jgeurten/Hollow-Organ/CAD/SLDPRTs/MCU_Battery_shield.SLDPRT

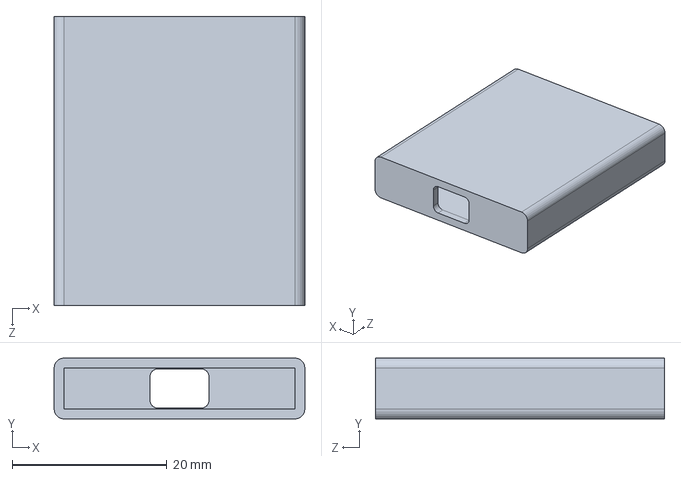
[picture p20: CAD file, 2017-09-10]
CAD/SLDPRTs/MCU_Battery_shield.SLDPRT
32.4 x 7.87 x 37.3 mm
