jgeurten/Hollow-Organ/CAD/SLDPRTs/pushbutton_panel.SLDPRT

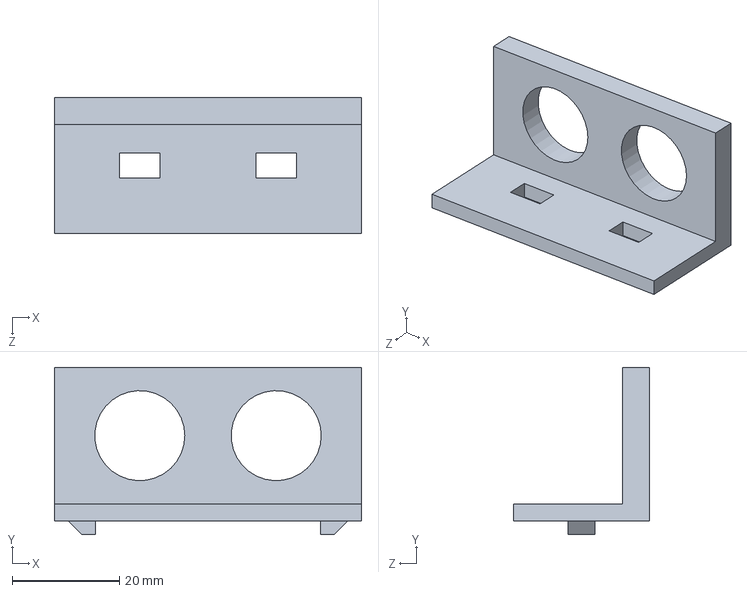
[picture p21: CAD file, 2017-09-10]
CAD/SLDPRTs/pushbutton_panel.SLDPRT
57.1 x 31.1 x 25.4 mm
