jgeurten/Hollow-Organ/CAD/SLDPRTs/bearing.SLDPRT

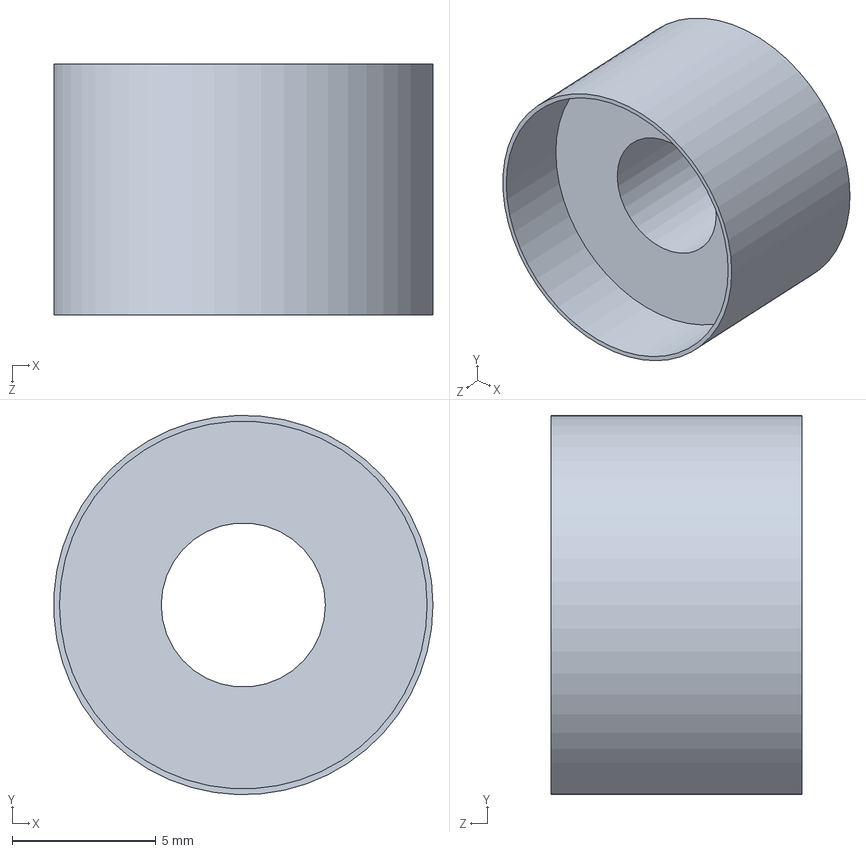
[picture p22: CAD file, 2017-09-10]
CAD/SLDPRTs/bearing.SLDPRT
13.2 x 13.2 x 8.74 mm
