jgeurten/Hollow-Organ/CAD/SLDPRTs/sphere.SLDPRT

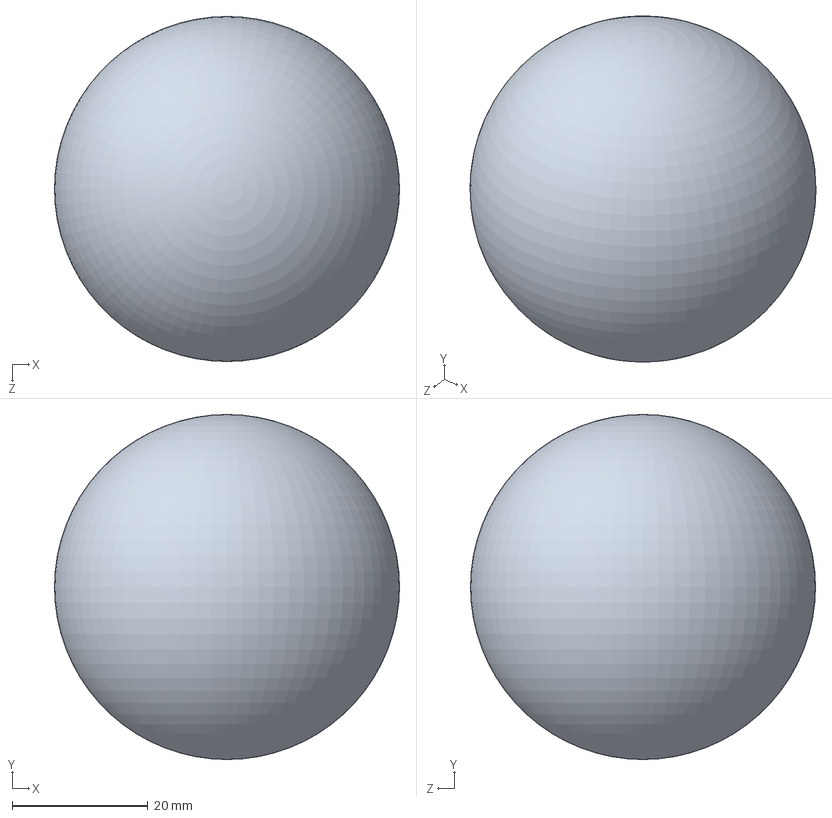
[picture p23: CAD file, 2017-09-10]
CAD/SLDPRTs/sphere.SLDPRT
50.8 x 50.8 x 50.8 mm
