jgeurten/Hollow-Organ/CAD/SLDPRTs/Face_Shaft_Collar_revE.SLDPRT

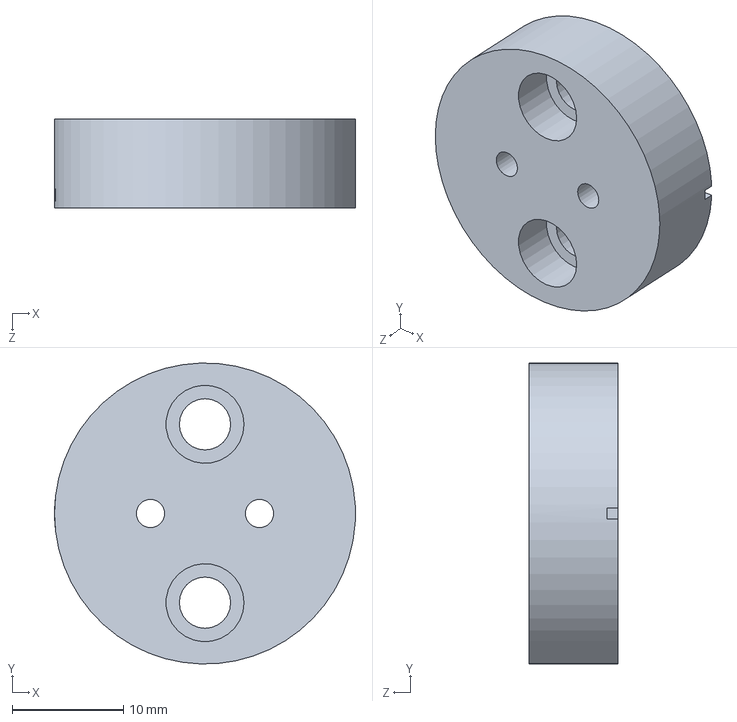
[picture p24: CAD file, 2017-09-10]
CAD/SLDPRTs/Face_Shaft_Collar_revE.SLDPRT
27.0 x 27.0 x 8.00 mm
