jgeurten/Hollow-Organ/CAD/SLDPRTs/Frame.SLDPRT

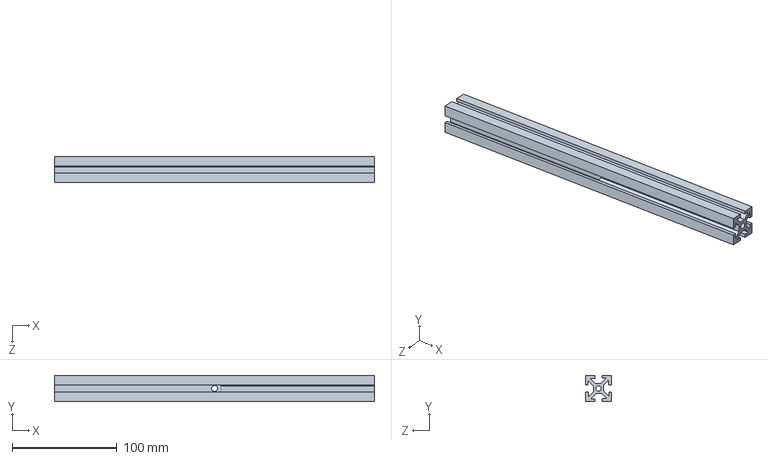
[picture p25: CAD file, 2017-09-10]
CAD/SLDPRTs/Frame.SLDPRT
304.8 x 25.2 x 25.2 mm
