jgeurten/Hollow-Organ/CAD/SLDPRTs/battery_shield.SLDPRT

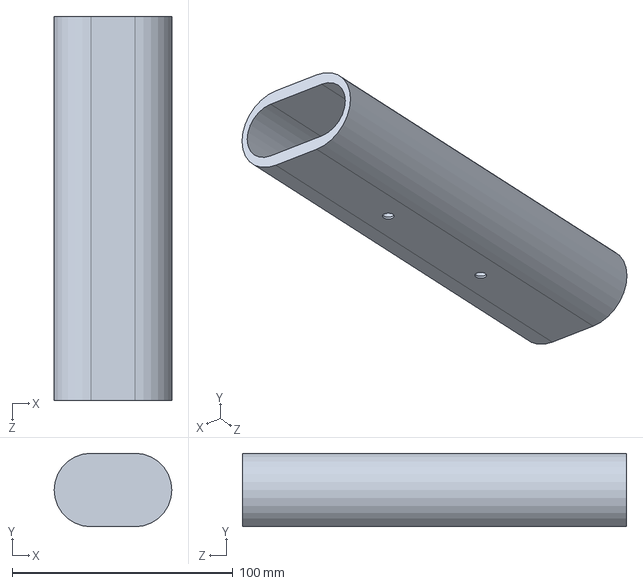
[picture p26: CAD file, 2017-09-10]
CAD/SLDPRTs/battery_shield.SLDPRT
53.3 x 33.3 x 174.0 mm
