jgeurten/Hollow-Organ/CAD/SLDPRTs/stepper_platform.SLDPRT

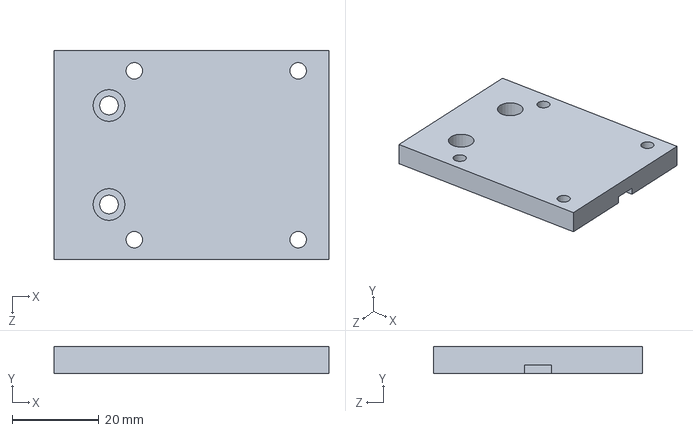
[picture p27: CAD file, 2017-09-10]
CAD/SLDPRTs/stepper_platform.SLDPRT
63.5 x 6.35 x 48.3 mm
