jgeurten/Hollow-Organ/CAD/SLDPRTs/mounting_plate.SLDPRT

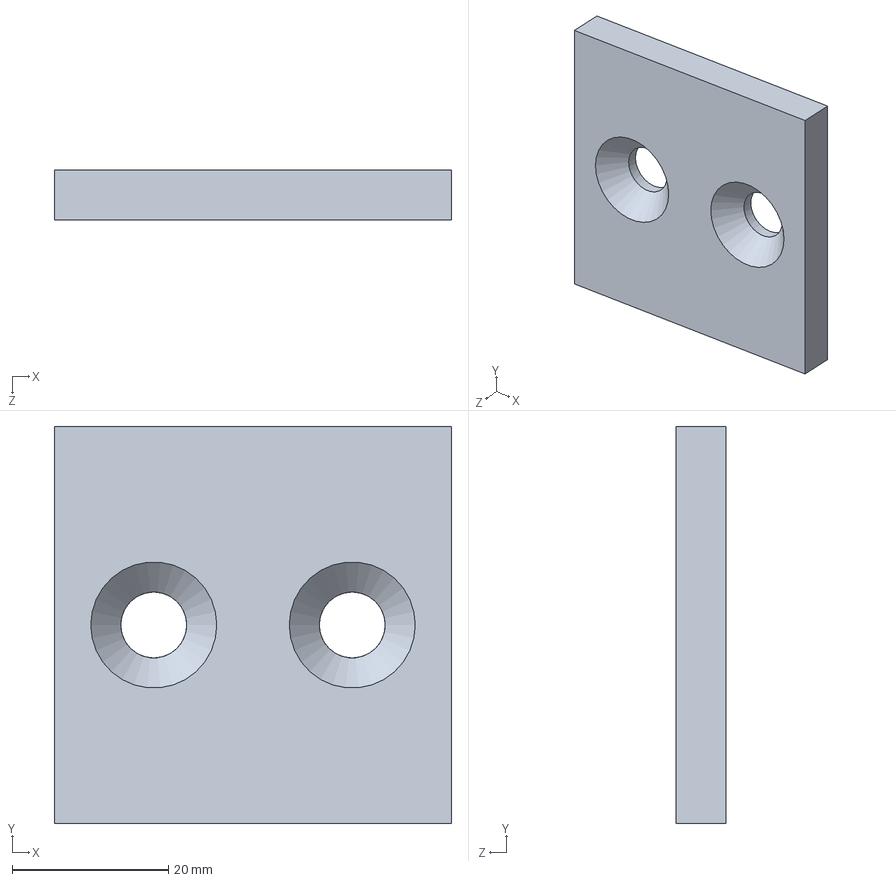
[picture p28: CAD file, 2017-07-20]
CAD/SLDPRTs/mounting_plate.SLDPRT
50.8 x 50.8 x 6.35 mm
