jgeurten/Hollow-Organ/CAD/SLDPRTs/threaded_four_arm_knob.SLDPRT

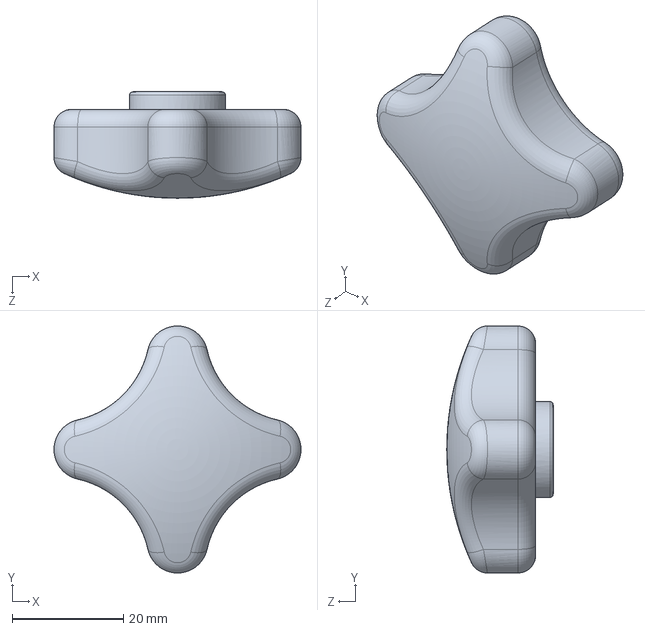
[picture p29: CAD file, 2017-07-20]
CAD/SLDPRTs/threaded_four_arm_knob.SLDPRT
44.4 x 44.4 x 19.2 mm
