jgeurten/Hollow-Organ/CAD/SLDPRTs/1_1_frame_22_inch.SLDPRT

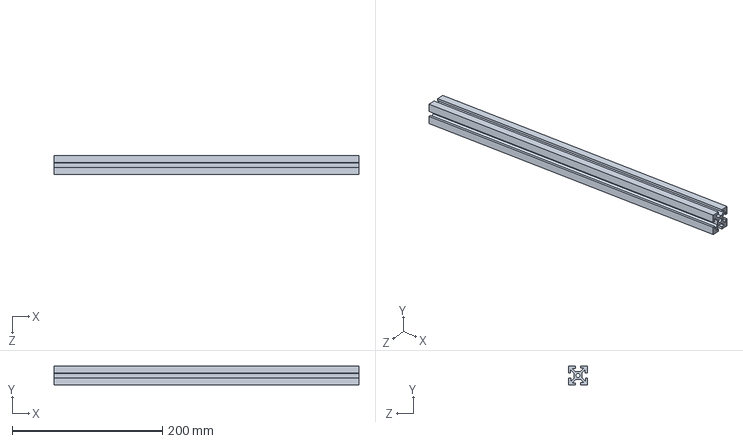
[picture p30: CAD file, 2017-07-20]
CAD/SLDPRTs/1_1_frame_22_inch.SLDPRT
406.4 x 25.2 x 25.2 mm
