jgeurten/Hollow-Organ/CAD/SLDPRTs/1by1by9inch_frame.SLDPRT

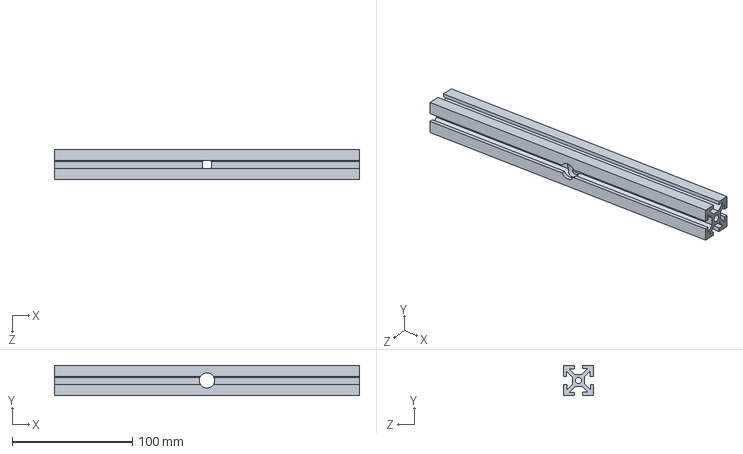
[picture p31: CAD file, 2017-07-20]
CAD/SLDPRTs/1by1by9inch_frame.SLDPRT
254.0 x 25.2 x 25.2 mm
