jgeurten/Hollow-Organ/CAD/SLDPRTs/stepper_bracket.SLDPRT

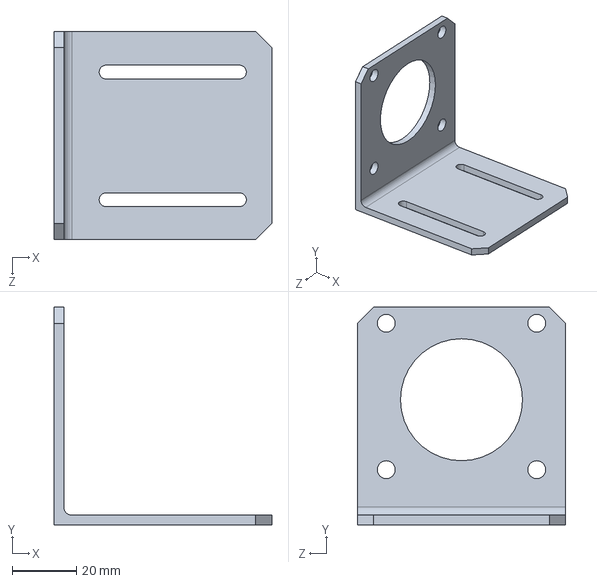
[picture p32: CAD file, 2017-07-20]
CAD/SLDPRTs/stepper_bracket.SLDPRT
68.1 x 68.1 x 65.0 mm
