jgeurten/Hollow-Organ/CAD/SLDPRTs/timing_belt_8inch.SLDPRT

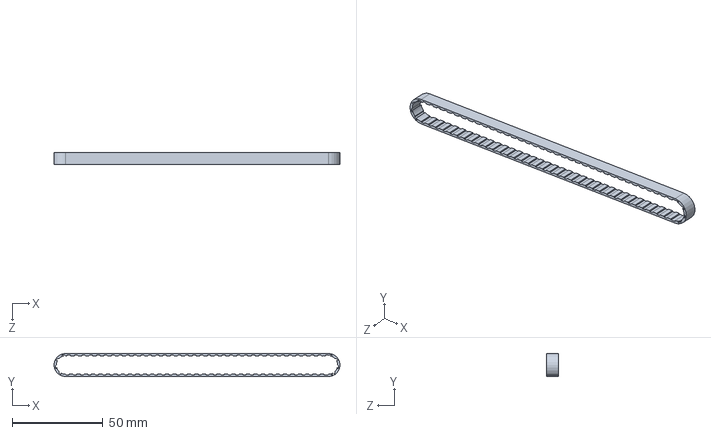
[picture p33: CAD file, 2017-07-20]
CAD/SLDPRTs/timing_belt_8inch.SLDPRT
157.5 x 12.7 x 6.35 mm
