jgeurten/Hollow-Organ/CAD/SLDPRTs/stepper_motor.SLDPRT

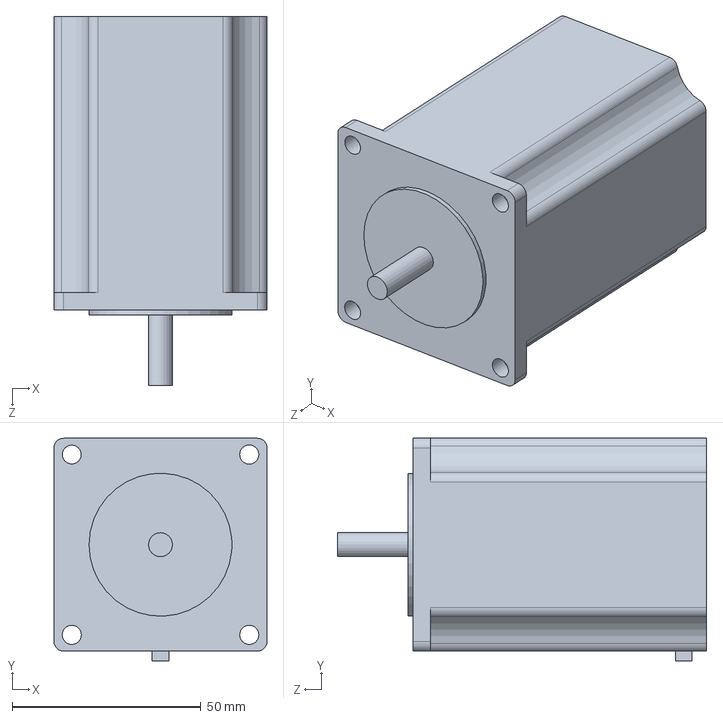
[picture p34: CAD file, 2017-07-20]
CAD/SLDPRTs/stepper_motor.SLDPRT
56.4 x 58.9 x 97.7 mm
