jgeurten/Hollow-Organ/CAD/SLDPRTs/Kidney_Mold.SLDPRT

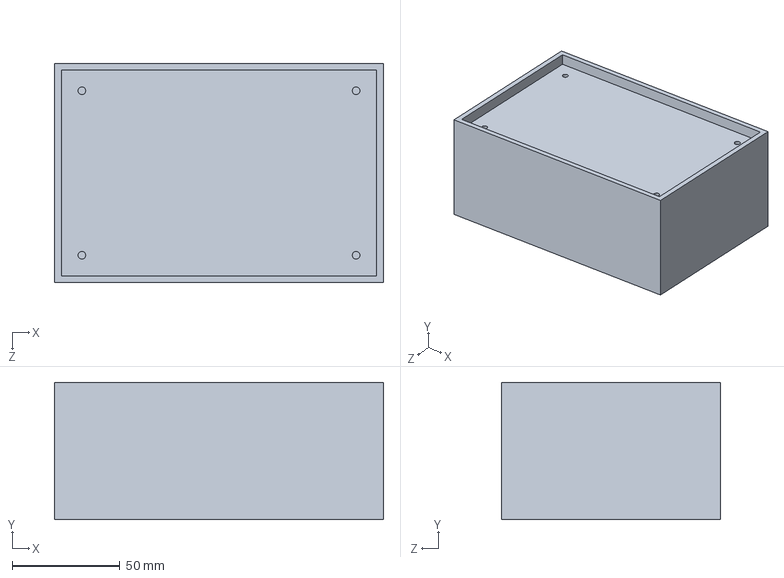
[picture p35: CAD file, 2017-07-20]
CAD/SLDPRTs/Kidney_Mold.SLDPRT
152.4 x 63.5 x 101.6 mm
