jgeurten/Hollow-Organ/CAD/SLDPRTs/1_1_frame_6_8inch.SLDPRT

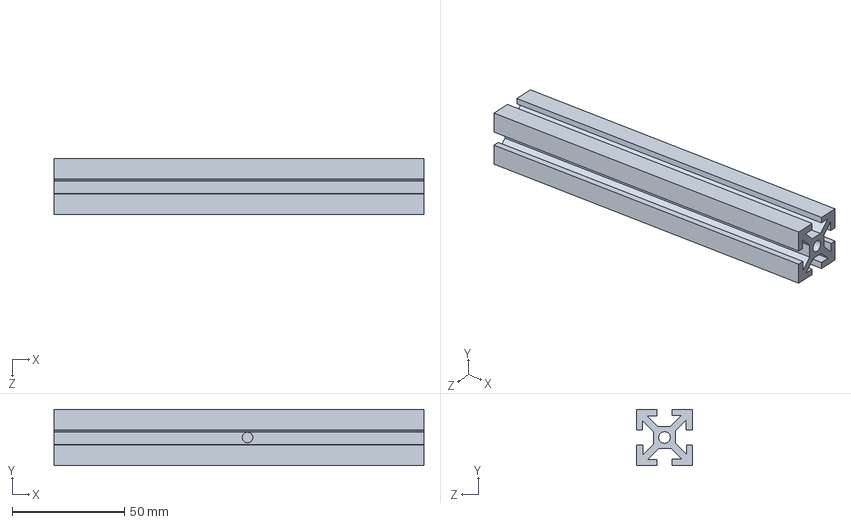
[picture p36: CAD file, 2017-07-20]
CAD/SLDPRTs/1_1_frame_6_8inch.SLDPRT
165.1 x 25.2 x 25.2 mm
