jgeurten/Hollow-Organ/CAD/SLDPRTs/1by1by11inch_frame.SLDPRT

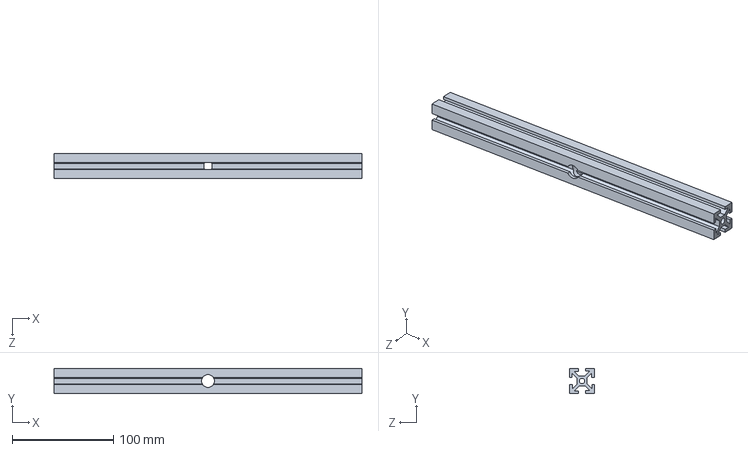
[picture p37: CAD file, 2017-07-20]
CAD/SLDPRTs/1by1by11inch_frame.SLDPRT
304.8 x 25.2 x 25.2 mm
