jgeurten/Hollow-Organ/CAD/SLDPRTs/DC_motor_L_bracket.SLDPRT

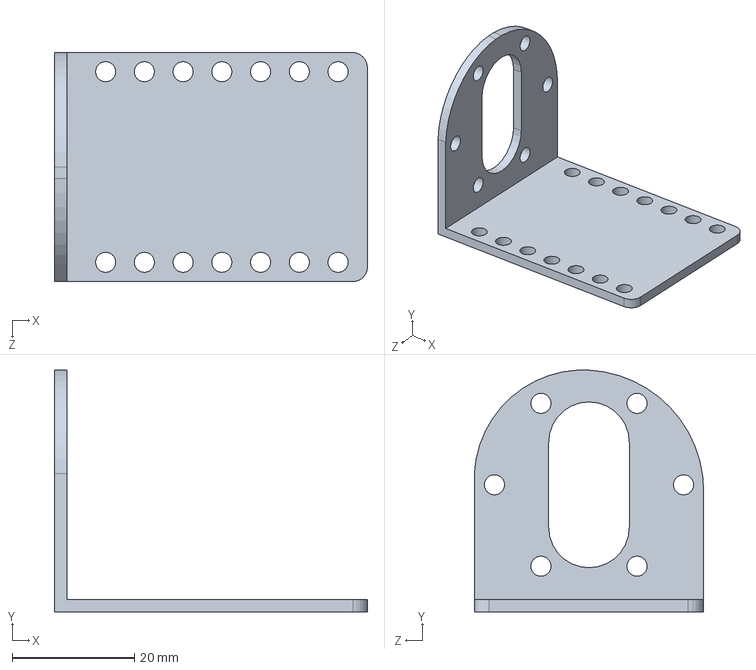
[picture p38: CAD file, 2017-07-20]
CAD/SLDPRTs/DC_motor_L_bracket.SLDPRT
51.3 x 39.6 x 37.6 mm
