jgeurten/Hollow-Organ/CAD/SLDPRTs/1_1_frame_7inch.SLDPRT

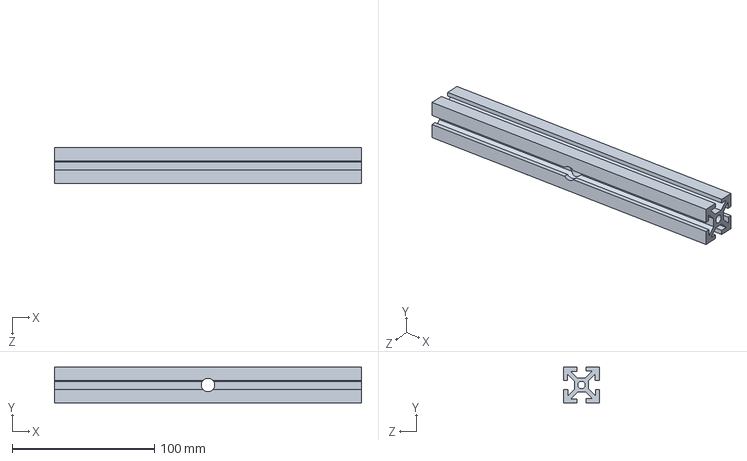
[picture p39: CAD file, 2017-07-20]
CAD/SLDPRTs/1_1_frame_7inch.SLDPRT
215.9 x 25.2 x 25.2 mm
