jgeurten/Hollow-Organ/CAD/SLDPRTs/timing_belt_9_5inch.SLDPRT

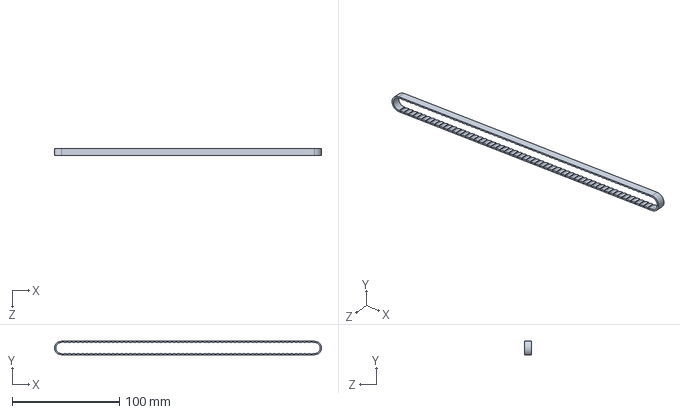
[picture p40: CAD file, 2017-07-20]
CAD/SLDPRTs/timing_belt_9_5inch.SLDPRT
248.9 x 12.7 x 6.35 mm
