jgeurten/Hollow-Organ/CAD/SLDPRTs/10-32_rod.SLDPRT

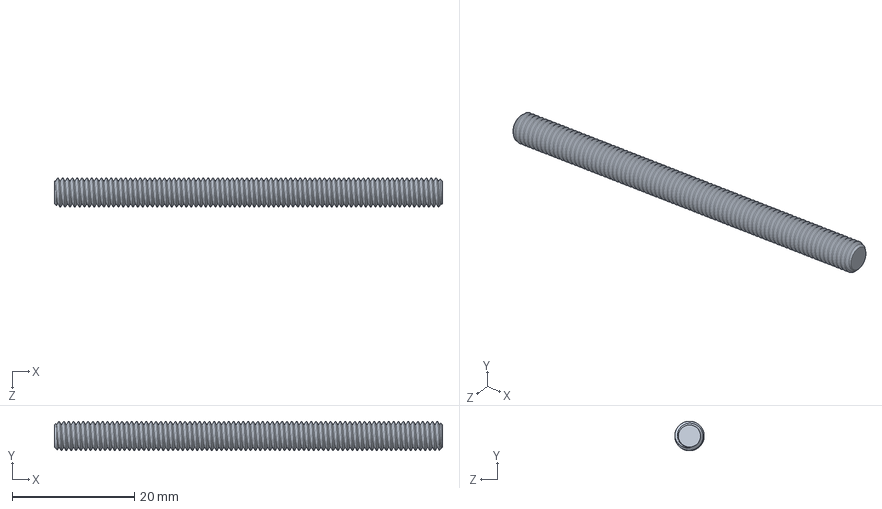
[picture p41: CAD file, 2017-07-20]
CAD/SLDPRTs/10-32_rod.SLDPRT
63.5 x 4.83 x 4.83 mm
