jgeurten/Hollow-Organ/CAD/SLDPRTs/1_1_frame_1_inch.SLDPRT

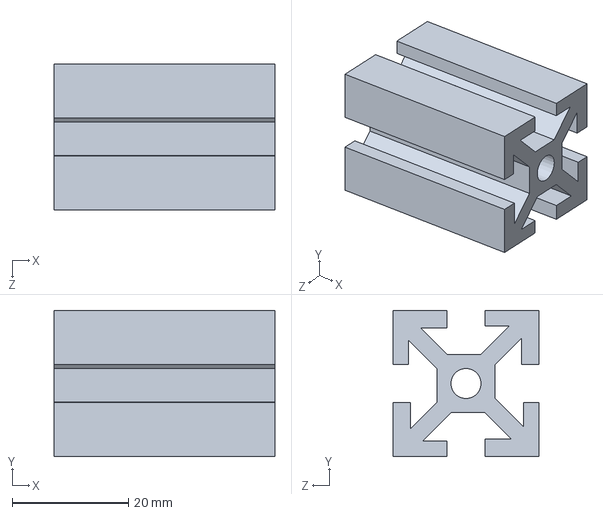
[picture p42: CAD file, 2017-07-20]
CAD/SLDPRTs/1_1_frame_1_inch.SLDPRT
38.1 x 25.2 x 25.2 mm
