jgeurten/Hollow-Organ/CAD/SLDPRTs/1_1_frame_true18_inch.SLDPRT

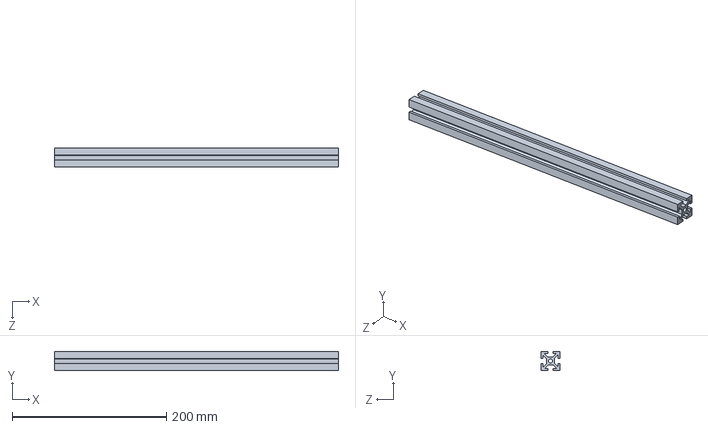
[picture p43: CAD file, 2017-07-20]
CAD/SLDPRTs/1_1_frame_true18_inch.SLDPRT
368.3 x 25.2 x 25.2 mm
