jgeurten/Hollow-Organ/CAD/SLDPRTs/framing_panel_inside.SLDPRT

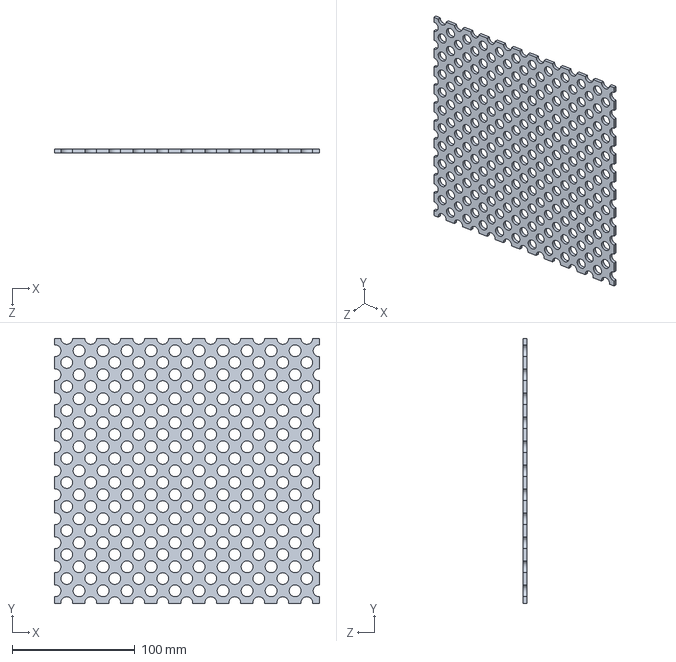
[picture p44: CAD file, 2017-07-20]
CAD/SLDPRTs/framing_panel_inside.SLDPRT
215.9 x 215.9 x 3.17 mm
