jgeurten/Hollow-Organ/CAD/SLDPRTs/Ball_Bearing.SLDPRT

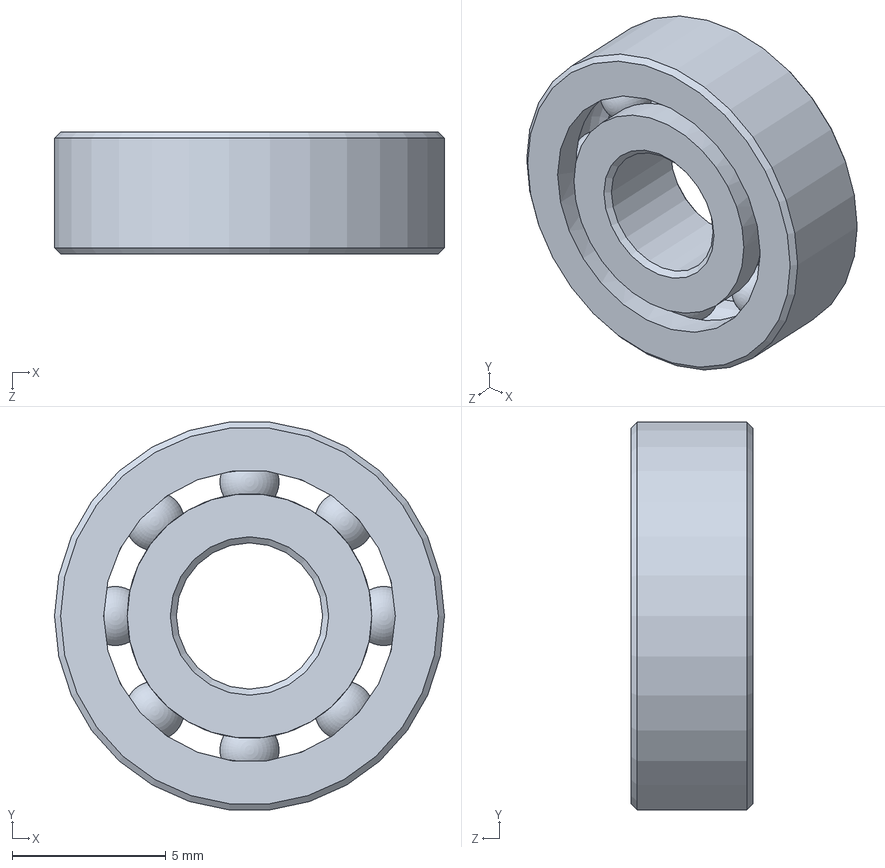
[picture p45: CAD file, 2017-06-14]
CAD/SLDPRTs/Ball_Bearing.SLDPRT
12.7 x 12.6 x 3.97 mm
