jgeurten/Hollow-Organ/CAD/SLDPRTs/Four_Arm_Knob.SLDPRT

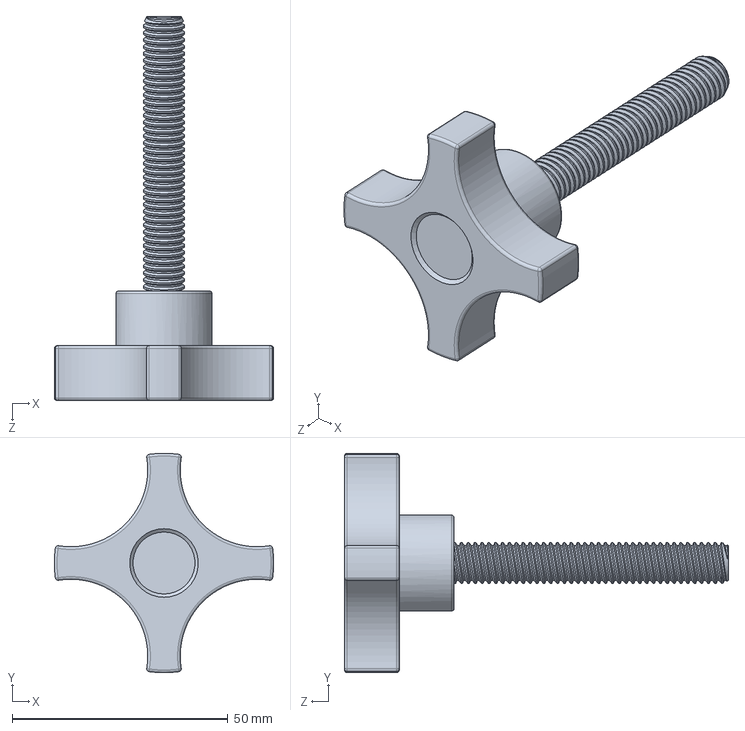
[picture p46: CAD file, 2017-06-14]
CAD/SLDPRTs/Four_Arm_Knob.SLDPRT
50.8 x 50.8 x 88.9 mm
