jgeurten/Hollow-Organ/CAD/SLDPRTs/Proto_board.SLDPRT

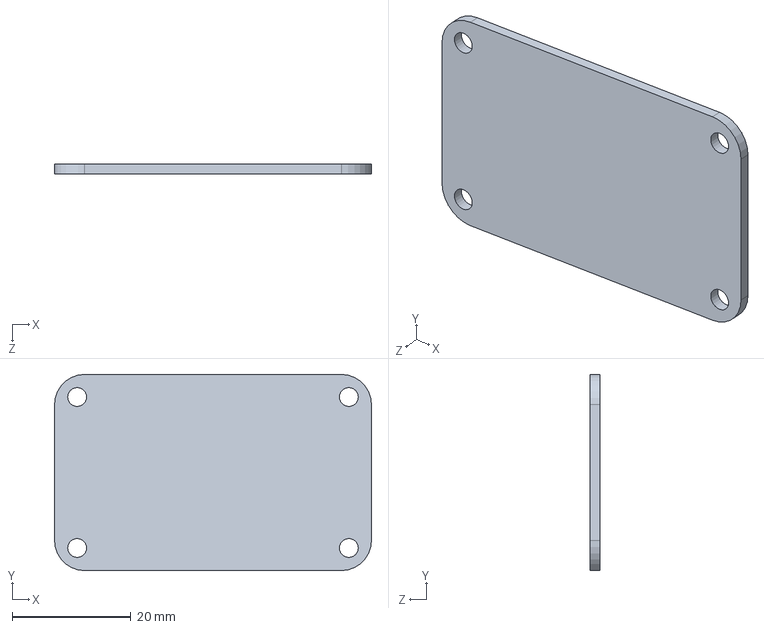
[picture p47: CAD file, 2017-06-14]
CAD/SLDPRTs/Proto_board.SLDPRT
53.3 x 33.0 x 1.60 mm
