jgeurten/Hollow-Organ/CAD/SLDPRTs/Hinge_1inch.SLDPRT

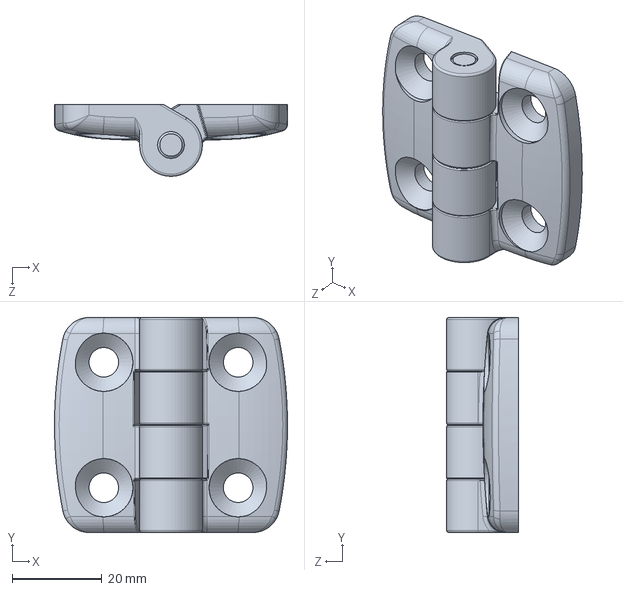
[picture p48: CAD file, 2017-06-14]
CAD/SLDPRTs/Hinge_1inch.SLDPRT
52.0 x 48.0 x 16.0 mm
