jgeurten/Hollow-Organ/CAD/SLDPRTs/corner_brace_1inch.SLDPRT

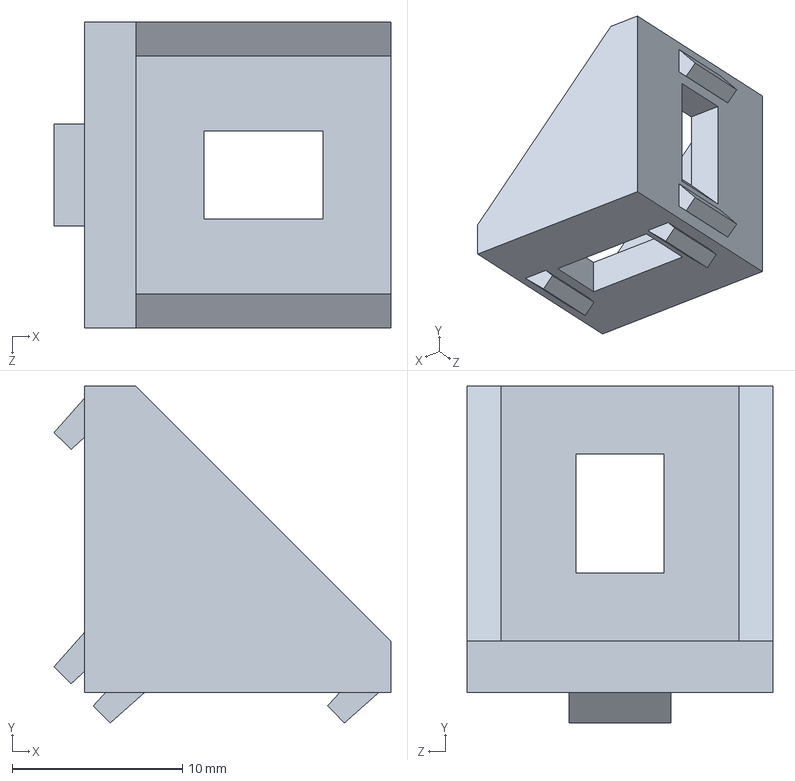
[picture p49: CAD file, 2017-06-14]
CAD/SLDPRTs/corner_brace_1inch.SLDPRT
19.8 x 19.8 x 18.0 mm
