jgeurten/Hollow-Organ/CAD/SLDPRTs/1_1_frame_18_inch.SLDPRT

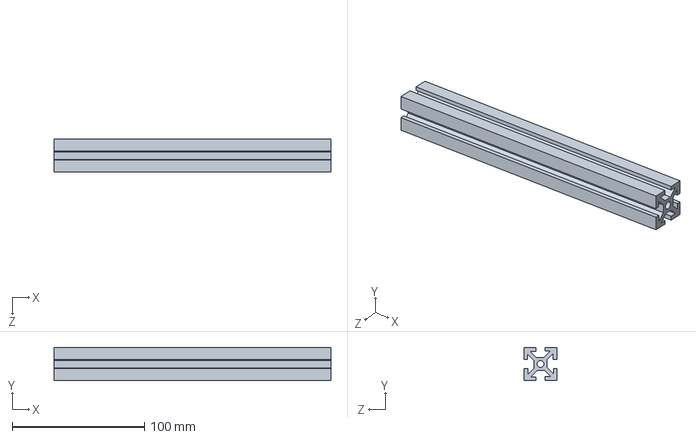
[picture p50: CAD file, 2017-06-14]
CAD/SLDPRTs/1_1_frame_18_inch.SLDPRT
209.5 x 25.2 x 25.2 mm
