jgeurten/Hollow-Organ/CAD/SLDPRTs/Knurled_Knob.SLDPRT

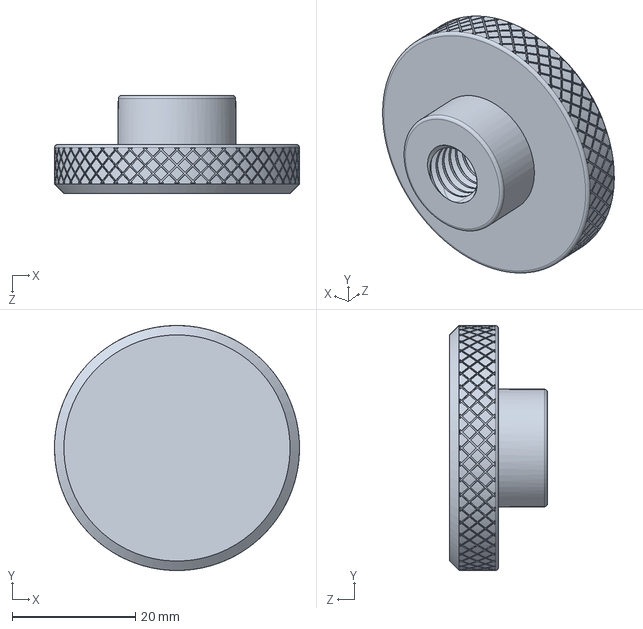
[picture p51: CAD file, 2017-06-14]
CAD/SLDPRTs/Knurled_Knob.SLDPRT
39.7 x 39.7 x 15.9 mm
