jgeurten/Hollow-Organ/CAD/SLDPRTs/timing_belt_pulley.SLDPRT

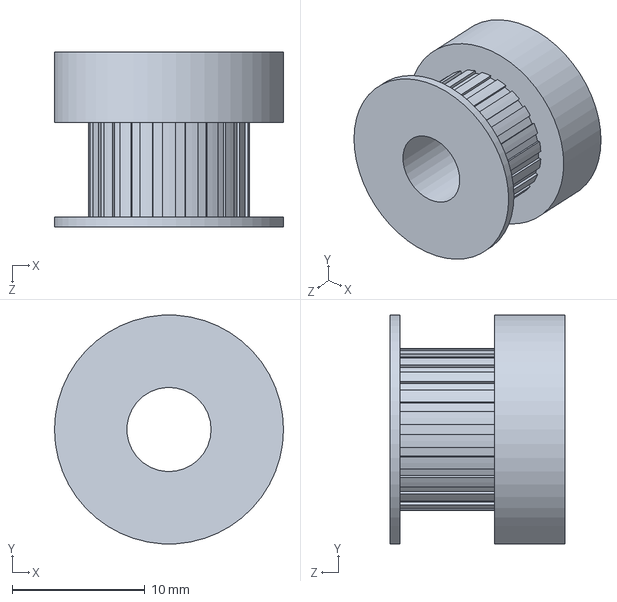
[picture p52: CAD file, 2017-06-14]
CAD/SLDPRTs/timing_belt_pulley.SLDPRT
17.3 x 17.2 x 13.2 mm
