jgeurten/Hollow-Organ/CAD/SLDPRTs/mounting_plate_rectangular.SLDPRT

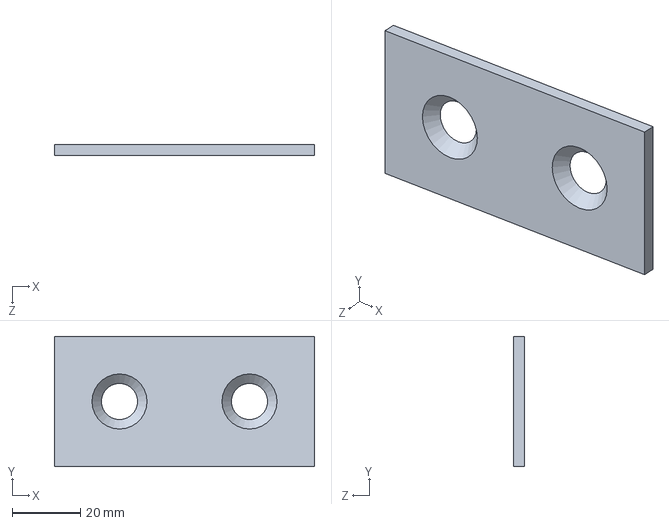
[picture p53: CAD file, 2017-06-14]
CAD/SLDPRTs/mounting_plate_rectangular.SLDPRT
76.2 x 38.1 x 3.17 mm
