jgeurten/Hollow-Organ/CAD/SLDPRTs/Threaded_Rod_Clamp.SLDPRT

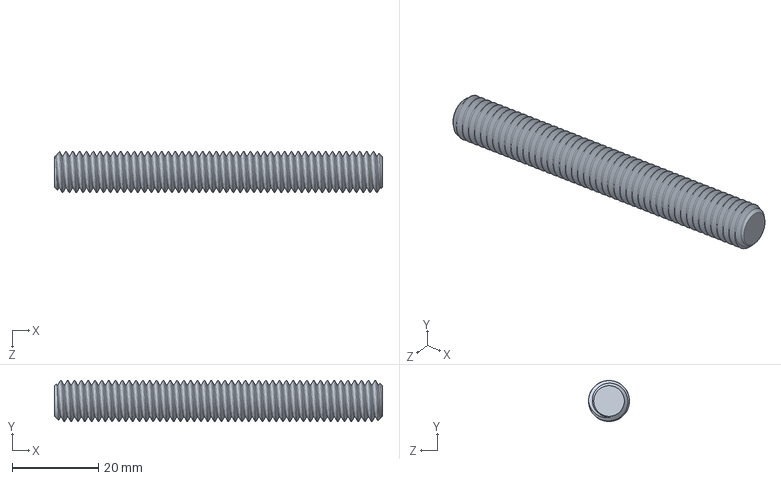
[picture p54: CAD file, 2017-06-14]
CAD/SLDPRTs/Threaded_Rod_Clamp.SLDPRT
76.2 x 9.53 x 9.53 mm
