jgeurten/Hollow-Organ/CAD/SLDPRTs/1by1by4_5inch_frame.SLDPRT

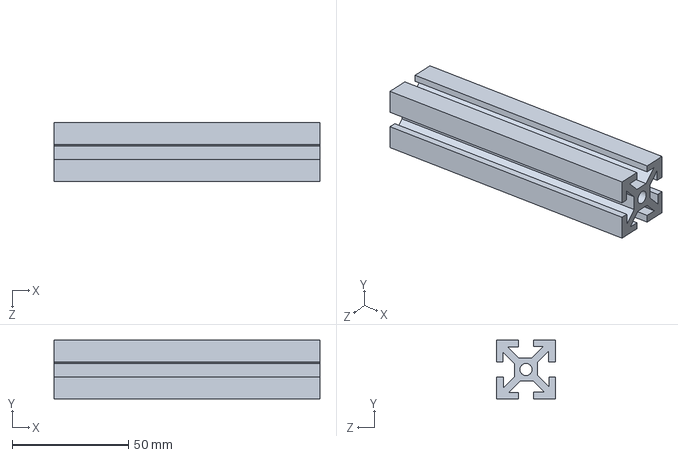
[picture p55: CAD file, 2017-06-14]
CAD/SLDPRTs/1by1by4_5inch_frame.SLDPRT
114.3 x 25.2 x 25.2 mm
