jgeurten/Hollow-Organ/CAD/SLDPRTs/shaft_spacer.SLDPRT

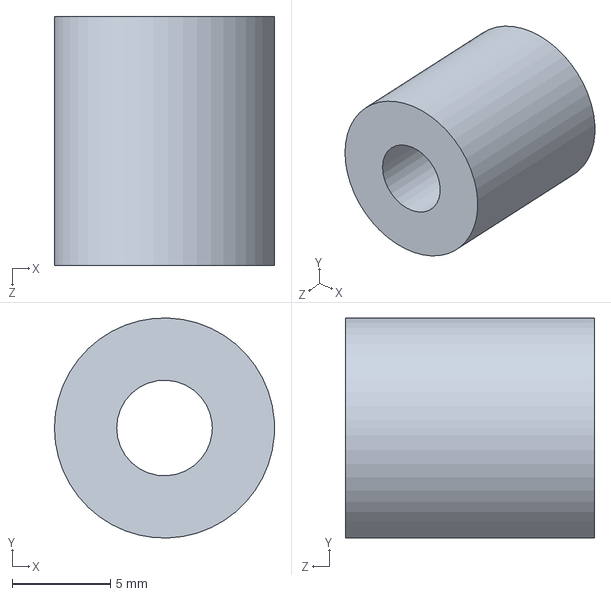
[picture p56: CAD file, 2017-06-14]
CAD/SLDPRTs/shaft_spacer.SLDPRT
11.2 x 11.2 x 12.7 mm
