jgeurten/Hollow-Organ/CAD/SLDPRTs/dc_12v_motor.SLDPRT

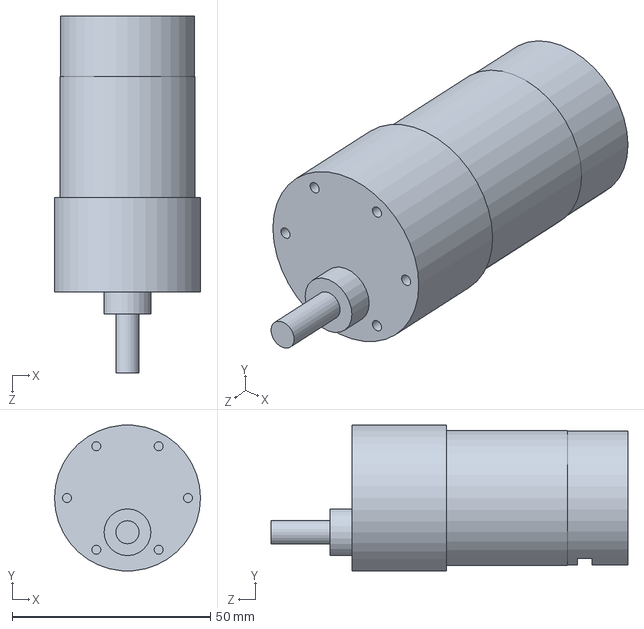
[picture p57: CAD file, 2017-06-14]
CAD/SLDPRTs/dc_12v_motor.SLDPRT
36.8 x 36.7 x 90.0 mm
