jgeurten/Hollow-Organ/CAD/SLDPRTs/encoder_stepper.SLDPRT

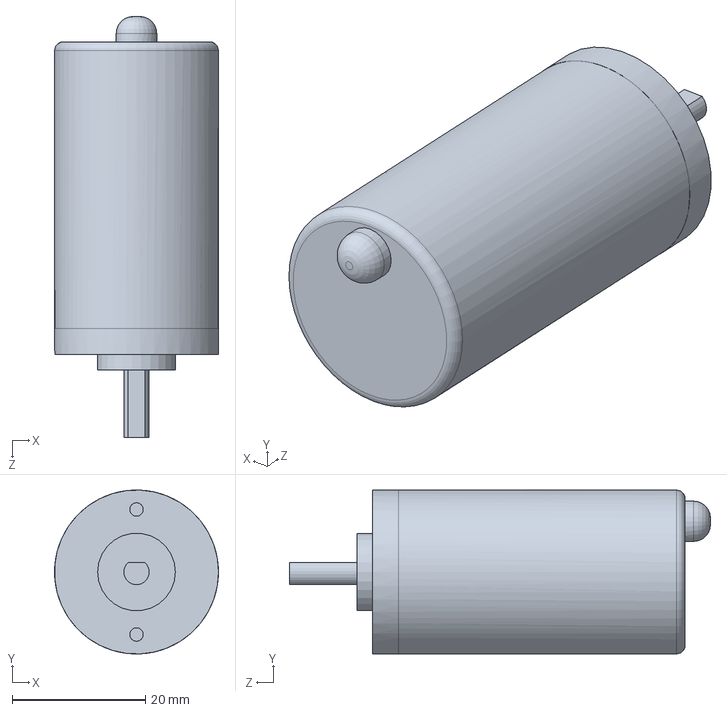
[picture p58: CAD file, 2017-06-14]
CAD/SLDPRTs/encoder_stepper.SLDPRT
24.6 x 24.6 x 63.2 mm
