jgeurten/Hollow-Organ/CAD/SLDPRTs/rotary_shaft.SLDPRT

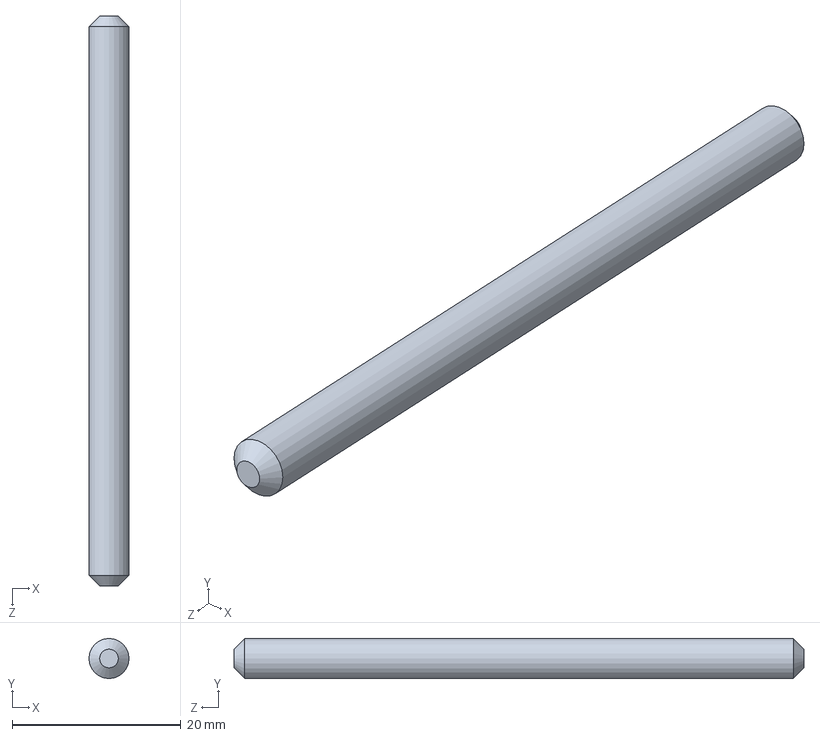
[picture p59: CAD file, 2017-06-14]
CAD/SLDPRTs/rotary_shaft.SLDPRT
4.76 x 4.76 x 67.6 mm
