jgeurten/Hollow-Organ/CAD/SLDPRTs/steel_shaft_3_16inch.SLDPRT

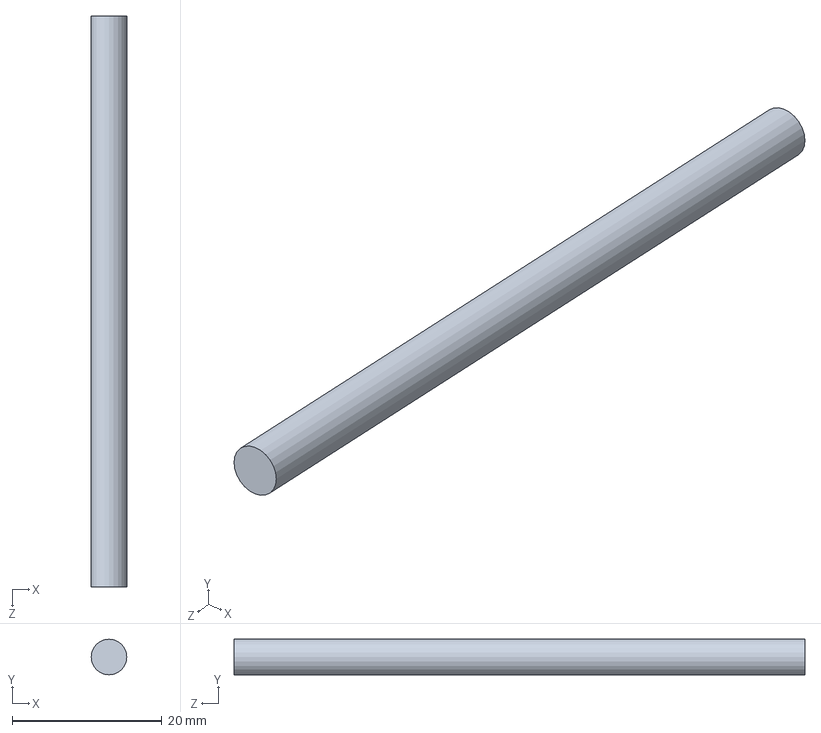
[picture p60: CAD file, 2017-06-14]
CAD/SLDPRTs/steel_shaft_3_16inch.SLDPRT
4.76 x 4.76 x 76.2 mm
