jgeurten/Hollow-Organ/CAD/SLDPRTs/1_1_frame_0_8_inch.SLDPRT

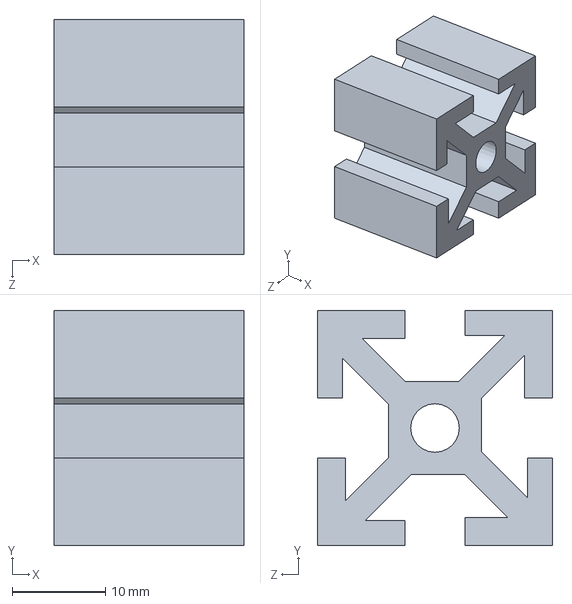
[picture p61: CAD file, 2017-06-14]
CAD/SLDPRTs/1_1_frame_0_8_inch.SLDPRT
20.3 x 25.2 x 25.2 mm
