jgeurten/Hollow-Organ/CAD/SLDPRTs/T-slotted_handle.SLDPRT

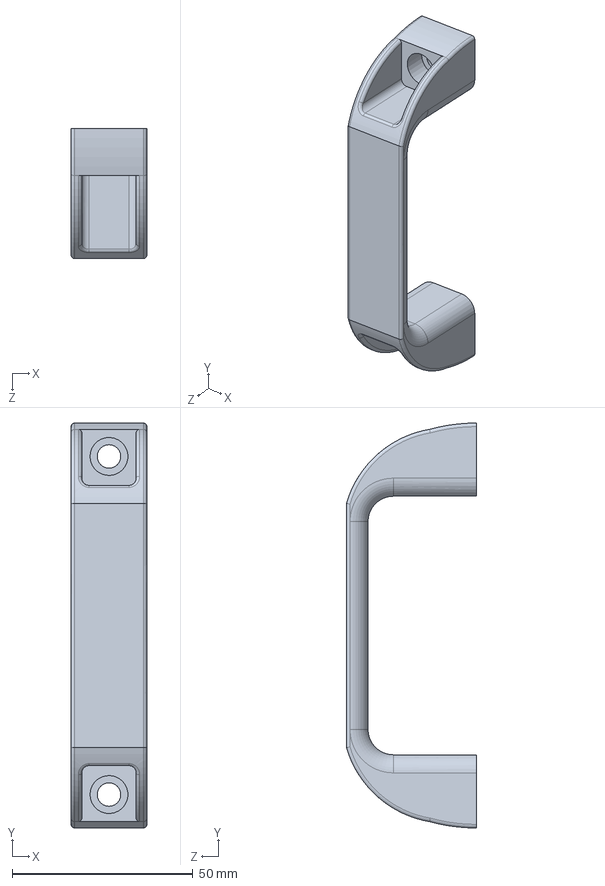
[picture p62: CAD file, 2017-06-14]
CAD/SLDPRTs/T-slotted_handle.SLDPRT
21.0 x 112.0 x 36.0 mm
