jgeurten/Hollow-Organ/CAD/SLDPRTs/steel_clamps.SLDPRT

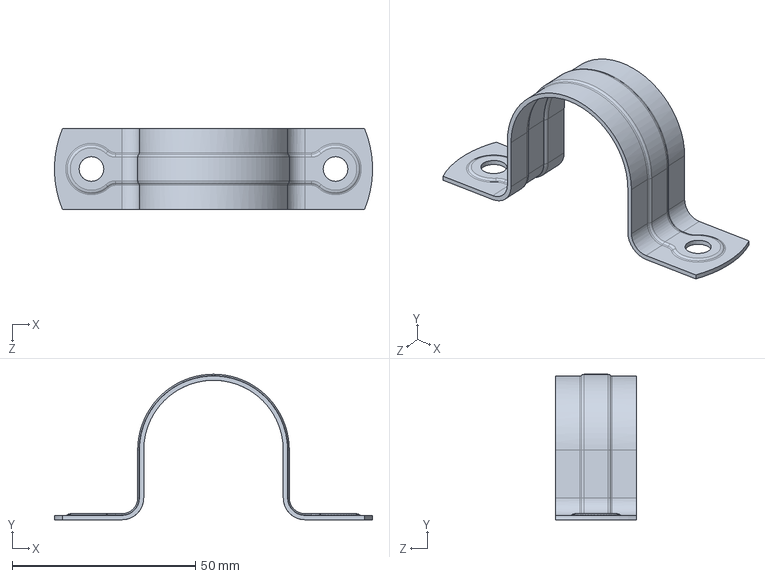
[picture p63: CAD file, 2017-06-14]
CAD/SLDPRTs/steel_clamps.SLDPRT
86.9 x 39.8 x 22.2 mm
